akuker/mAcTX_Quadra_840av/images/IMG_9528.jpg

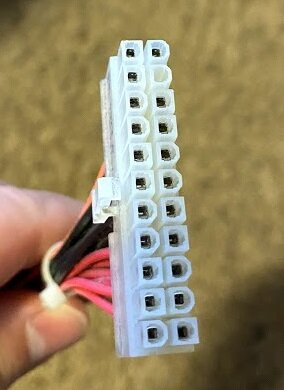
images/IMG_9528.jpg
