akuker/mAcTX_Quadra_840av/images/IMG_9530.jpg

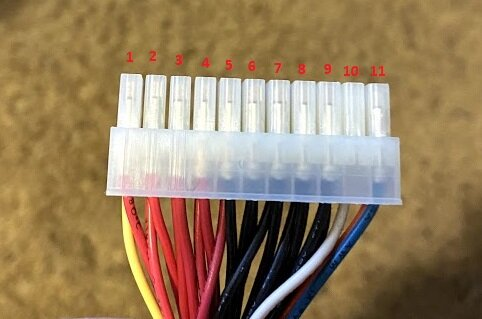
images/IMG_9530.jpg
